svenpetersen1965/PET_CBM_1541_Adapter/Rev. 0/Pictures/0079_-_format_SD2IEC.JPG

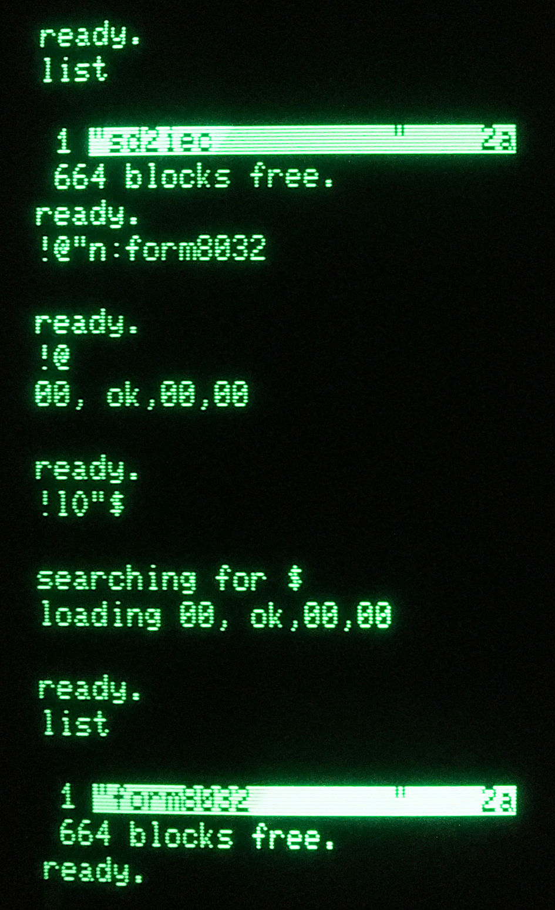
Rev. 0/Pictures/0079_-_format_SD2IEC.JPG
