svenpetersen1965/PET_CBM_1541_Adapter/Rev. 0/Pictures/0137_-_status_1581.JPG

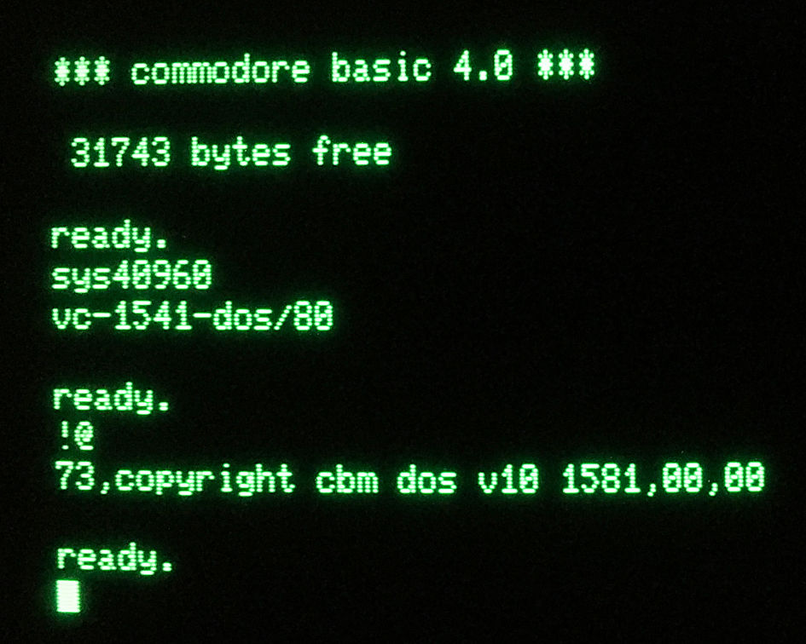
Rev. 0/Pictures/0137_-_status_1581.JPG
