svenpetersen1965/PET_CBM_1541_Adapter/Rev. 0/Pictures/9884(_-_SYS_status_catalog.JPG

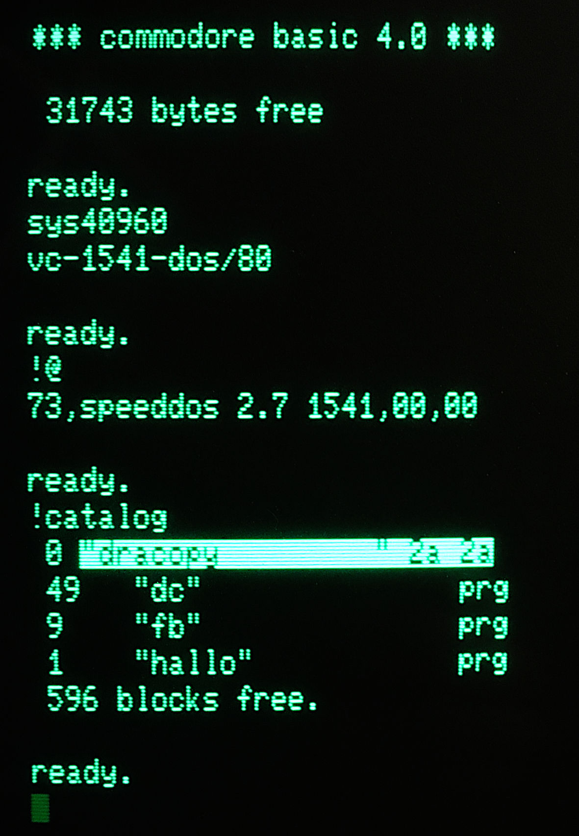
Rev. 0/Pictures/9884(_-_SYS_status_catalog.JPG
