svenpetersen1965/PET_CBM_1541_Adapter/Rev. 0/Pictures/9901_-_catalog.JPG

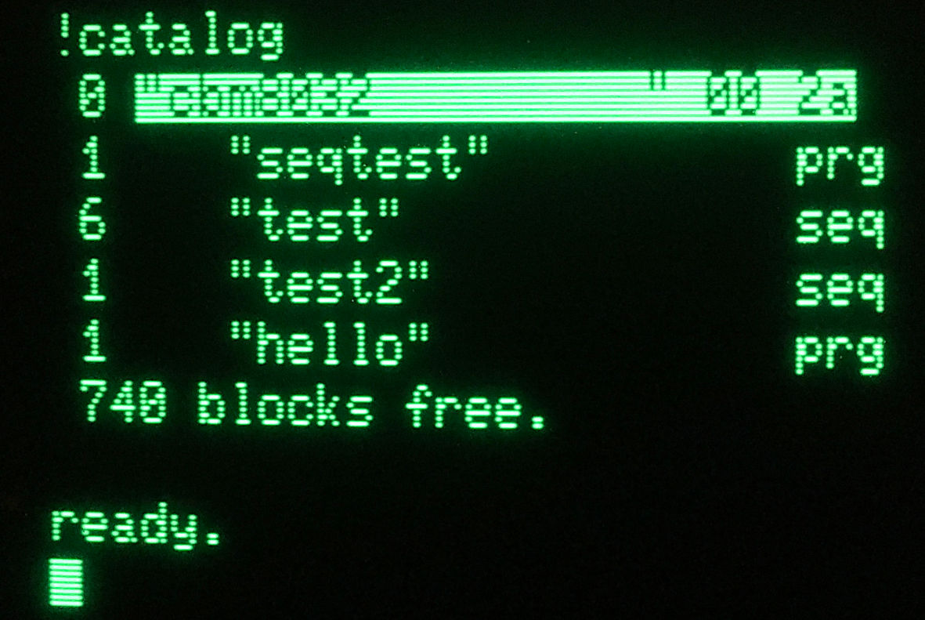
Rev. 0/Pictures/9901_-_catalog.JPG
