svenpetersen1965/PET_CBM_1541_Adapter/3D-print_case/Rev. 0/Label/Label_barrel.png

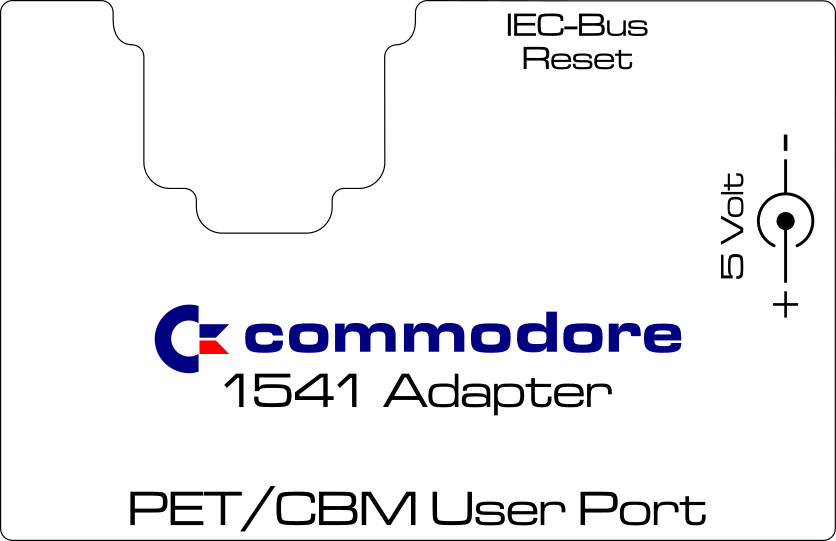
3D-print_case/Rev. 0/Label/Label_barrel.png
