svenpetersen1965/PET_CBM_1541_Adapter/Rev. 0/Pictures/9900_-_loadsaveverify.JPG

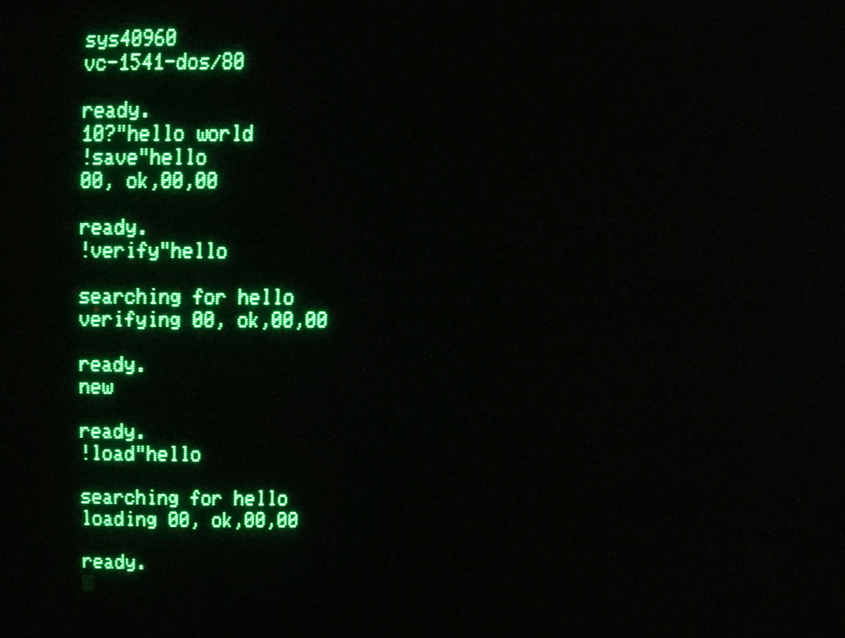
Rev. 0/Pictures/9900_-_loadsaveverify.JPG
