svenpetersen1965/PET_CBM_1541_Adapter/Rev. 0/Pictures/Pi1541_test_seq.png

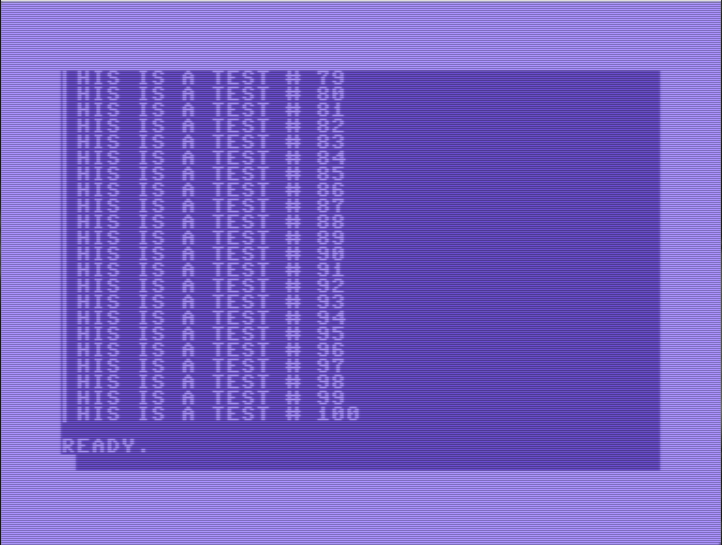
Rev. 0/Pictures/Pi1541_test_seq.png
